kamilix2003/Phase-Shifter/Src/beam_controller.c

#include "beam_controller.h"
#include "util/soft_timer.h"

error_t beam_controller_init(beam_controller_t* controller, const beam_controller_config_t* config) {
    error_t err;

    // Initialize the phase shifter manager
    err = phase_shifter_manager_init(&controller->phase_shifter_manager, config->hspi);
    if (err != STATUS_OK) {
        return err;
    }

    // Initialize the button interface
    err = button_interface_init(&controller->button_interface);
    if (err != STATUS_OK) {
        return err;
    }

    err = com_interface_init(&controller->com_interface);
    if (err != STATUS_OK) {
        return err;
    }

    return STATUS_OK;
}

error_t beam_controller_update(beam_controller_t* controller) {
    error_t err;

    // Update the phase shifter manager
    err = phase_shifter_manager_update(&controller->phase_shifter_manager);
    if (err != STATUS_OK) {
        return err;
    }

    // Update the button interface
    err = button_interface_update(&controller->button_interface);
    if (err != STATUS_OK) {
        return err;
    }

    err = com_interface_update(&controller->com_interface);
    if (err != STATUS_OK) {
        return err;
    }

    return STATUS_OK;
}
